sporkus/le_capybara_keyboard/plate/36-keys/plate_36keys-top.jpg

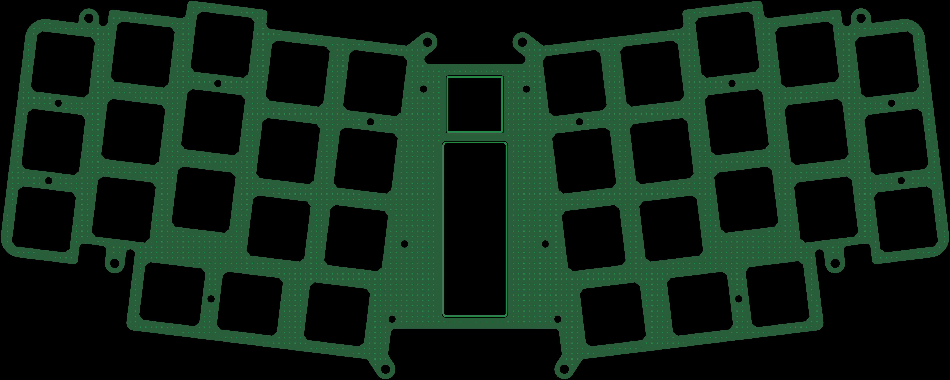
plate/36-keys/plate_36keys-top.jpg
